ErikGoldman/hornetcockpit/FilesToPrint/UFC/UFC desk Back Plate.3mf

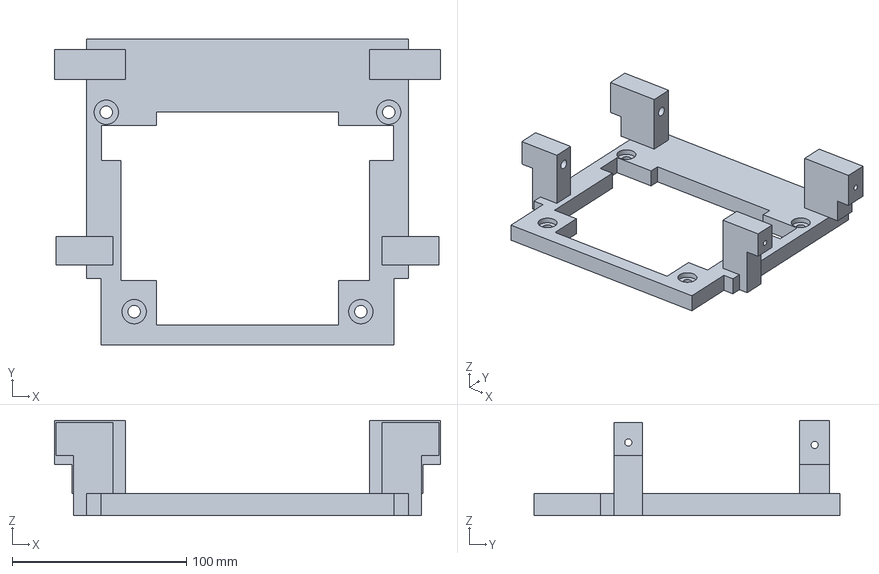
[picture p24: CAD file, 2024-12-28]
FilesToPrint/UFC/UFC desk Back Plate.3mf
221.3 x 175.3 x 54.6 mm
