ErikGoldman/hornetcockpit/FilesToPrint/DDI/DDI desk mount clamps.3mf

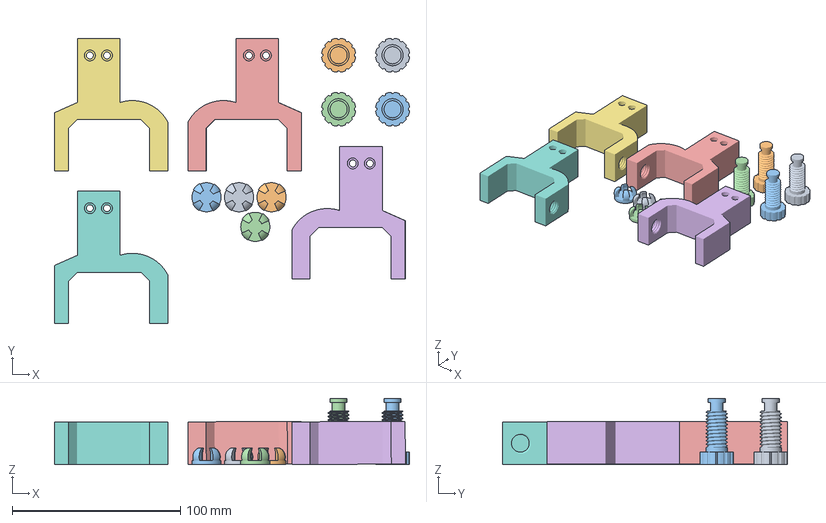
[picture p25: CAD file, 2024-12-28]
FilesToPrint/DDI/DDI desk mount clamps.3mf
211.2 x 169.8 x 39.4 mm
bolt x 4
DDI desk mount arm right x 2
DDI desk mount arm left x 2
ddi desk mount bolt head x 4
