ErikGoldman/hornetcockpit/FilesToPrint/Master arm panel/master arm fake pcb.3mf

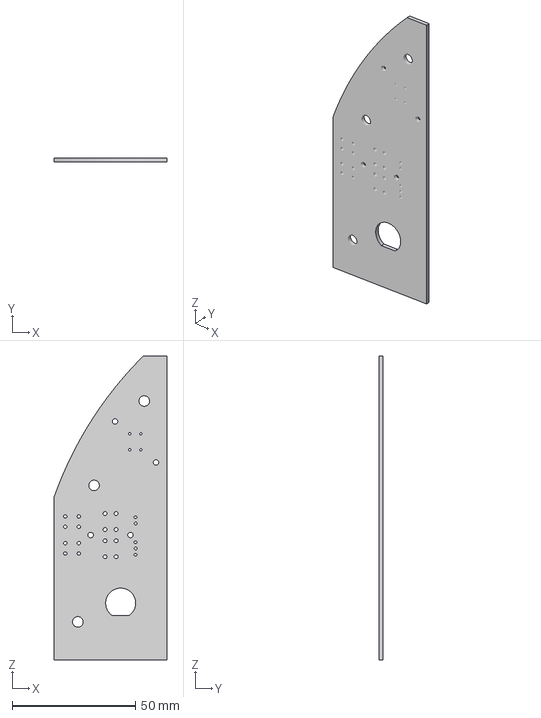
[picture p26: CAD file, 2024-12-28]
FilesToPrint/Master arm panel/master arm fake pcb.3mf
45.7 x 1.60 x 123.5 mm
