ErikGoldman/hornetcockpit/FilesToPrint/UFC/ufc spacer plate.3mf

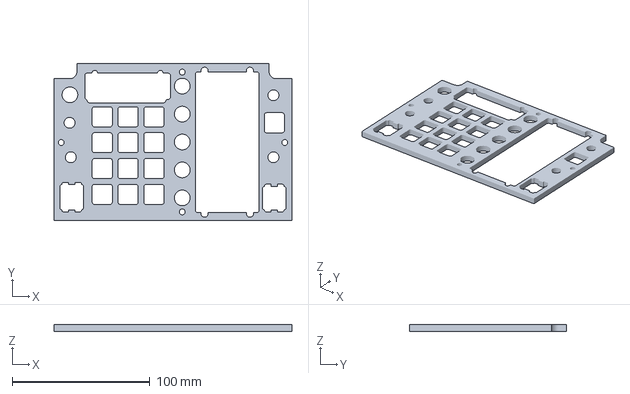
[picture p27: CAD file, 2024-11-20]
FilesToPrint/UFC/ufc spacer plate.3mf
173.0 x 114.3 x 4.76 mm
