ErikGoldman/hornetcockpit/FilesToPrint/Master arm panel/master arm desk extension.3mf

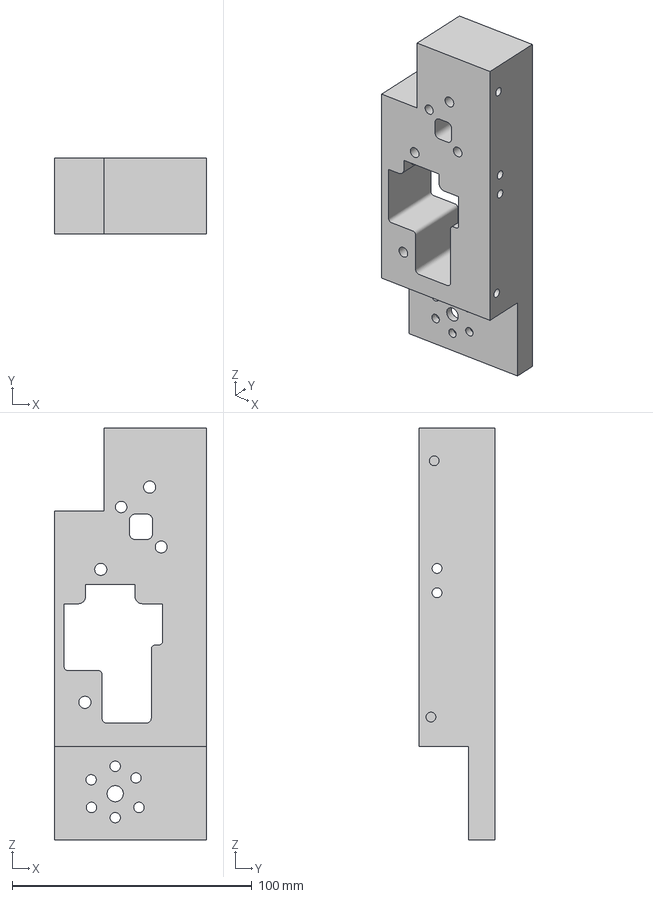
[picture p28: CAD file, 2024-12-28]
FilesToPrint/Master arm panel/master arm desk extension.3mf
63.5 x 31.8 x 171.8 mm
