ErikGoldman/hornetcockpit/FilesToPrint/UFC/ufc buttons.3mf

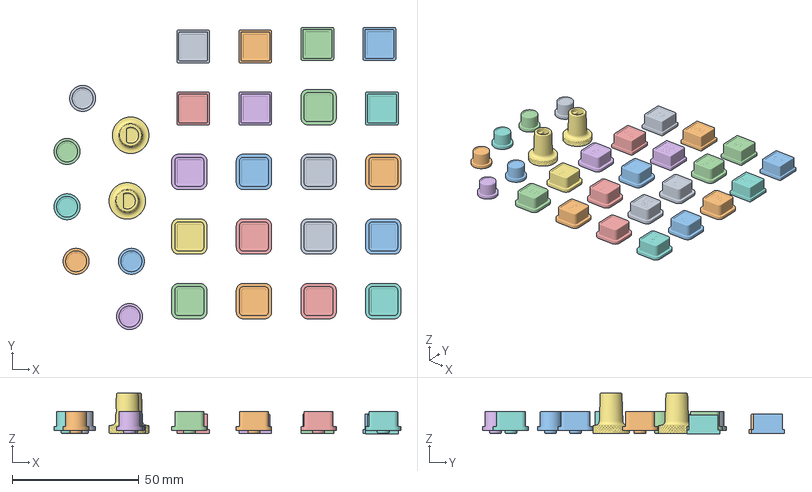
[picture p29: CAD file, 2024-11-20]
FilesToPrint/UFC/ufc buttons.3mf
136.7 x 119.1 x 16.1 mm
RESN_OH1A8A1-110_UFC SQUARE BUTTON, EMCON_-_V41
RESN_OH1A8A1-128_UFC SQUARE BUTTON, ENT_-_V41
RESN_OH1A8A1-124_UFC SQUARE BUTTON, 0_-_V41
RESN_OH1A8A1-120_UFC SQUARE BUTTON, CLR_-_V41
RESN_OH1A8A1-127_UFC SQUARE BUTTON, 9_-_V41
RESN_OH1A8A1-123_UFC SQUARE BUTTON, 8_-_V41
RESN_OH1A8A1-119_UFC SQUARE BUTTON, 7_-_V41
RESN_OH1A8A1-126_UFC SQUARE BUTTON, 6_-_V41
RESN_OH1A8A1-122_UFC SQUARE BUTTON, 5_-_V41
RESN_OH1A8A1-118_UFC SQUARE BUTTON, 4_-_V41
RESN_OH1A8A1-125_UFC SQUARE BUTTON, 3_-_V41
RESN_OH1A8A1-121_UFC SQUARE BUTTON, 2_-_V41
RESN_OH1A8A1-109_UFC SQUARE BUTTON, 1_-_v41
RESN_OH1A8A1-112_UFC ROUND BUTTON_-_V41 x 6
RESN_OH1A8A1-12_UFC COMM KNOB_-_V19 x 2
RESN_OH1A8A3-14 - AP SQUARE BUTTON, AP_-_v10
RESN_OH1A8A3-16 - AP SQUARE BUTTON, IFF_-_v10
RESN_OH1A8A3-17 - AP SQUARE BUTTON, TCN_-_v10
RESN_OH1A8A3-18 - AP SQUARE BUTTON, ILS_-_v10
RESN_OH1A8A3-19 - AP SQUARE BUTTON, DL_-_v10
RESN_OH1A8A3-20 - AP SQUARE BUTTON, BCN_-_v10
RESN_OH1A8A3-21 - AP SQUARE BUTTON, ON-OFF_-_v10
