ErikGoldman/hornetcockpit/FilesToPrint/DDI/ddi back.3mf

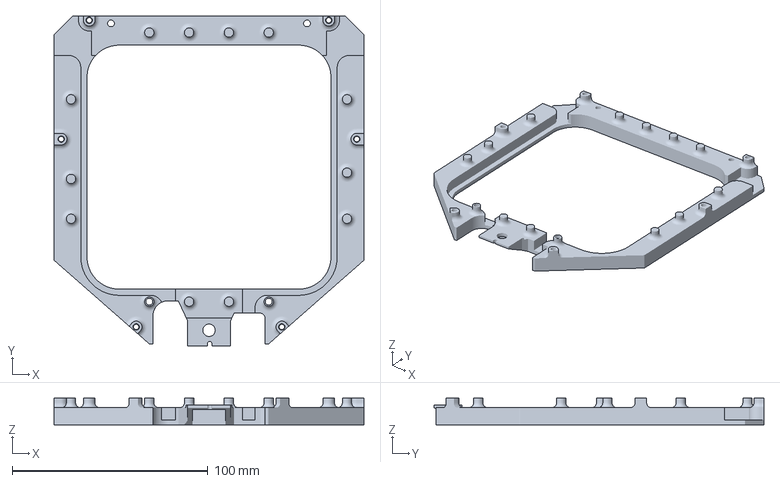
[picture p30: CAD file, 2024-11-20]
FilesToPrint/DDI/ddi back.3mf
158.2 x 168.2 x 13.6 mm
