ErikGoldman/hornetcockpit/FilesToPrint/UFC/ufc backplate.3mf

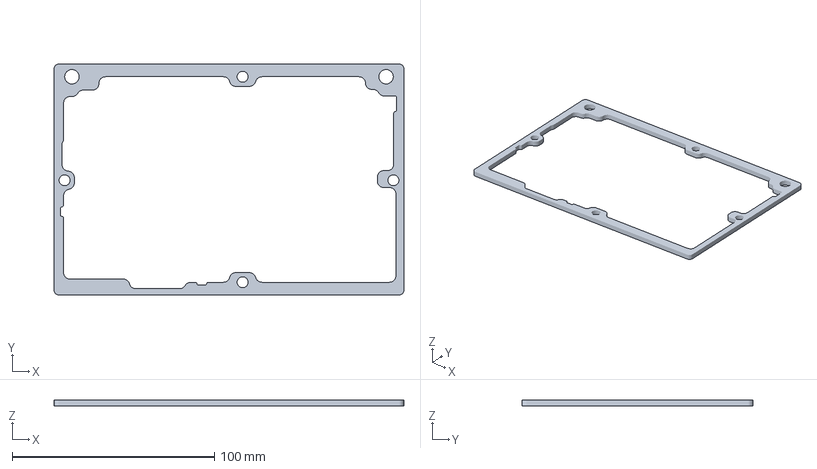
[picture p31: CAD file, 2024-11-20]
FilesToPrint/UFC/ufc backplate.3mf
173.0 x 114.3 x 3.17 mm
