ErikGoldman/hornetcockpit/FilesToPrint/DDI/ddi button accessories.3mf

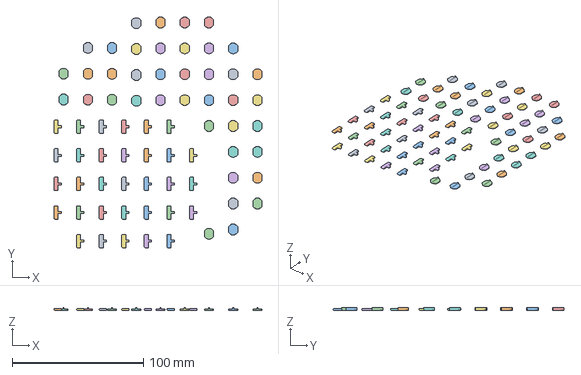
[picture p32: CAD file, 2024-11-20]
FilesToPrint/DDI/ddi button accessories.3mf
158.7 x 176.1 x 2.16 mm
RESN_OH1A3-17_DDI-FINGERGUARDS_-_V8
ddi button insert
