ErikGoldman/hornetcockpit/FilesToPrint/UFC/ufc top panel.3mf

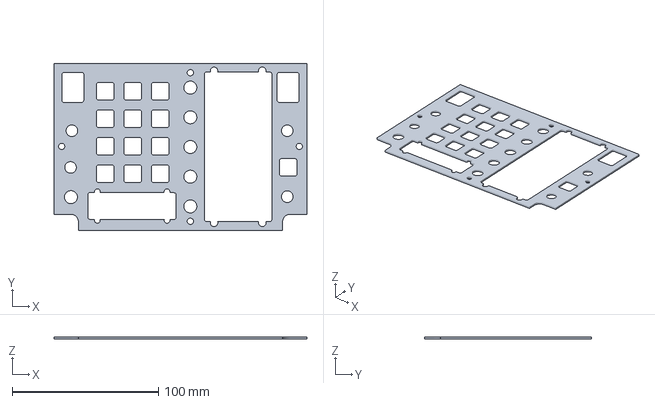
[picture p33: CAD file, 2024-11-20]
FilesToPrint/UFC/ufc top panel.3mf
173.0 x 114.3 x 1.59 mm
