ErikGoldman/hornetcockpit/FilesToPrint/UFC/ufc button guards.3mf

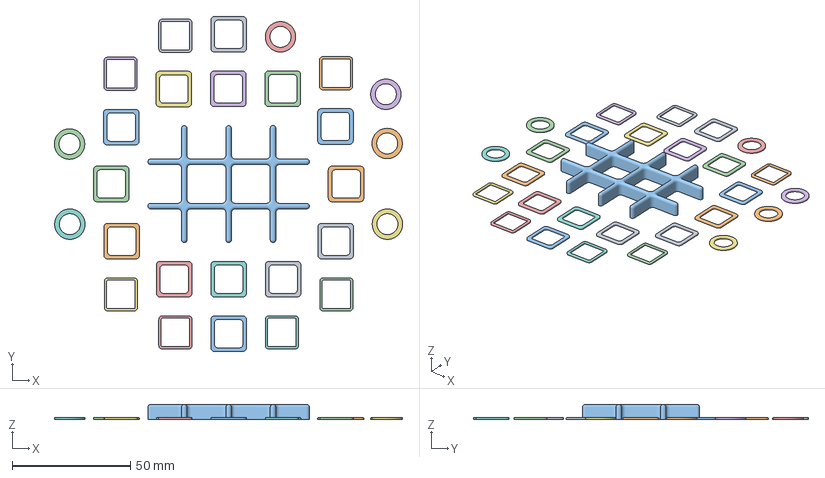
[picture p34: CAD file, 2024-11-20]
FilesToPrint/UFC/ufc button guards.3mf
147.5 x 141.9 x 6.35 mm
RESN_OH1A8A1-111_UFC SQUARE BUTTON TRIM_-_V41 x 14
RESN_OH1A8A1-113_UFC ROUND BUTTON GUARD_-_V41 x 6
RESN_OH1A8A1-116_UFC FINGER GUARD_-_V33
RESN_OH1A8A3-22 - AP SQUARE BUTTON TRIM_-_v10 x 7
